AsociacionMakerLevante/Prototipo_ESP32-C3-LCD/Imagenes/S0.jpg

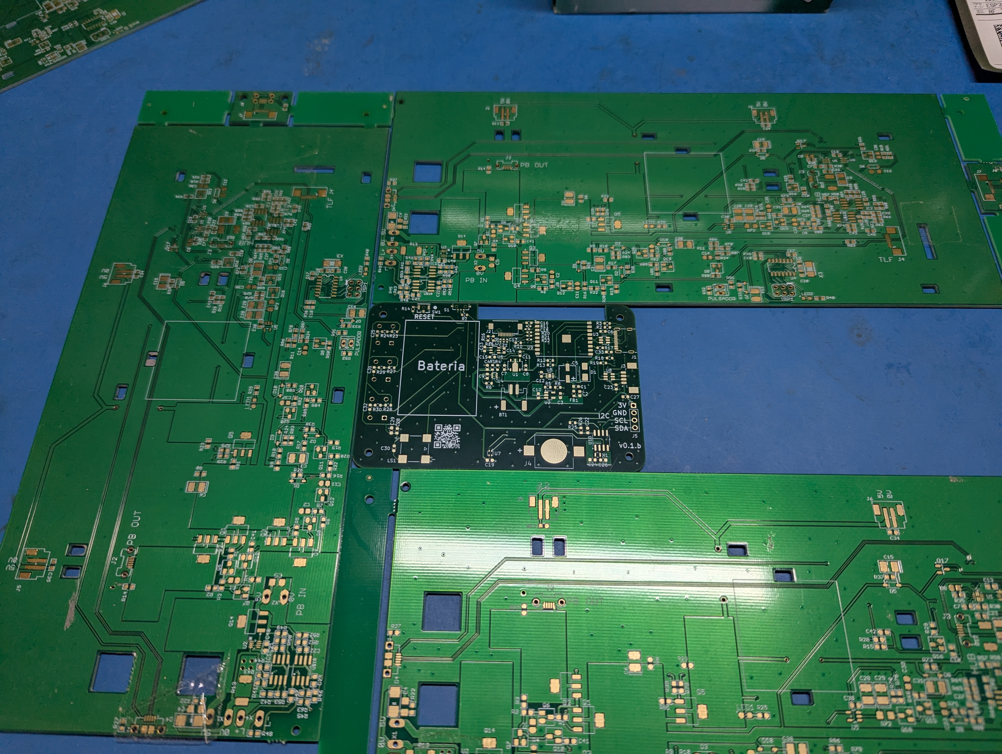
Imagenes/S0.jpg
