AsociacionMakerLevante/Prototipo_ESP32-C3-LCD/Imagenes/S00.jpg

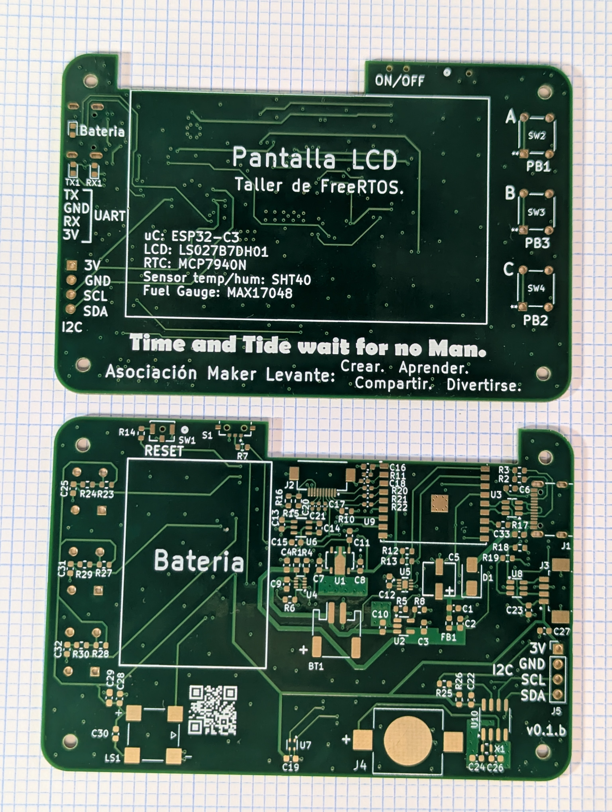
Imagenes/S00.jpg
