AsociacionMakerLevante/Prototipo_ESP32-C3-LCD/Imagenes/S1.jpg

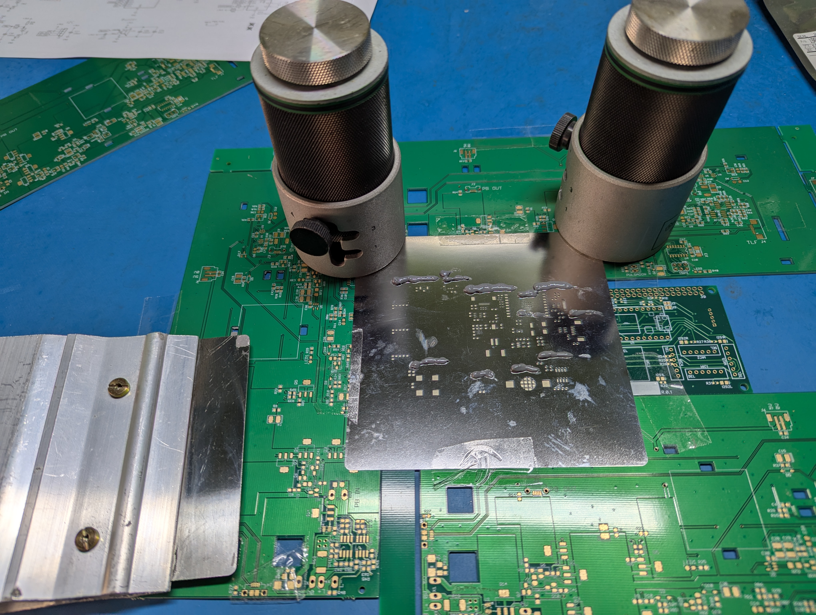
Imagenes/S1.jpg
