AsociacionMakerLevante/Prototipo_ESP32-C3-LCD/Imagenes/S4.jpg

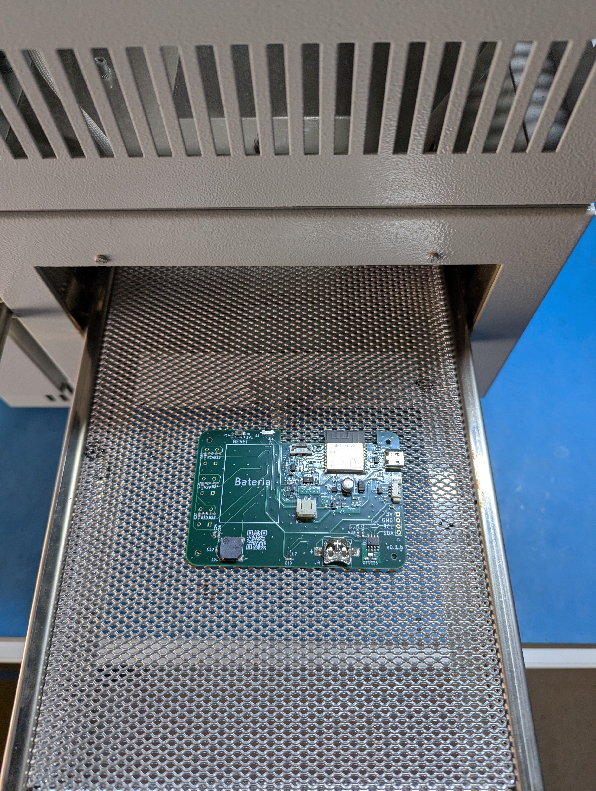
Imagenes/S4.jpg
