AsociacionMakerLevante/Prototipo_ESP32-C3-LCD/Imagenes/S6.jpg

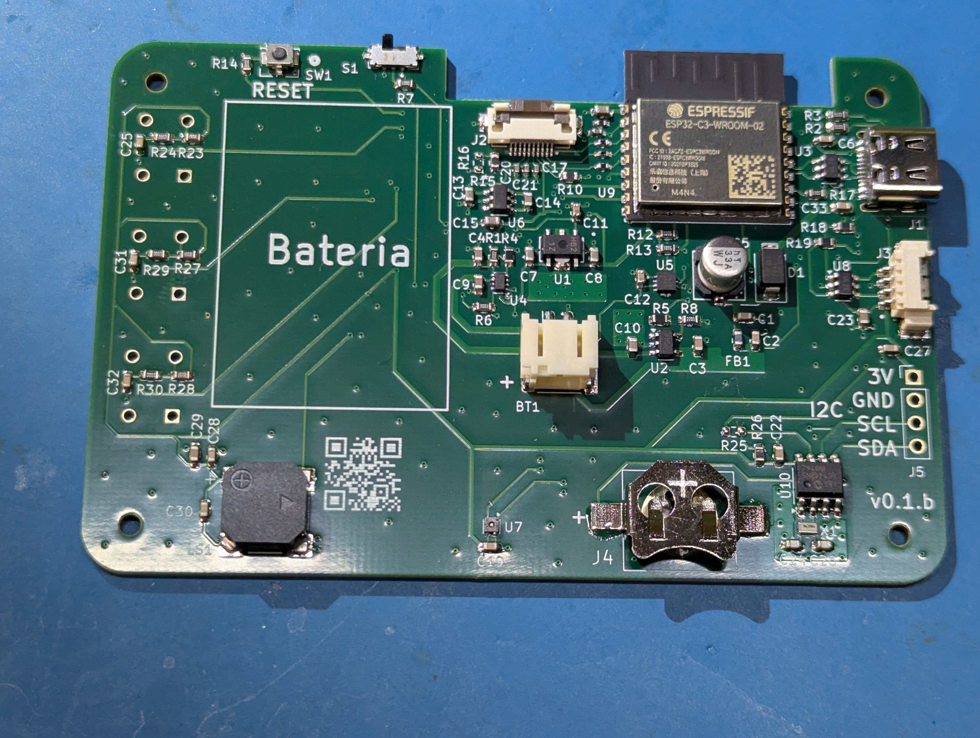
Imagenes/S6.jpg
