AsociacionMakerLevante/Prototipo_ESP32-C3-LCD/Imagenes/Bateria.jpg

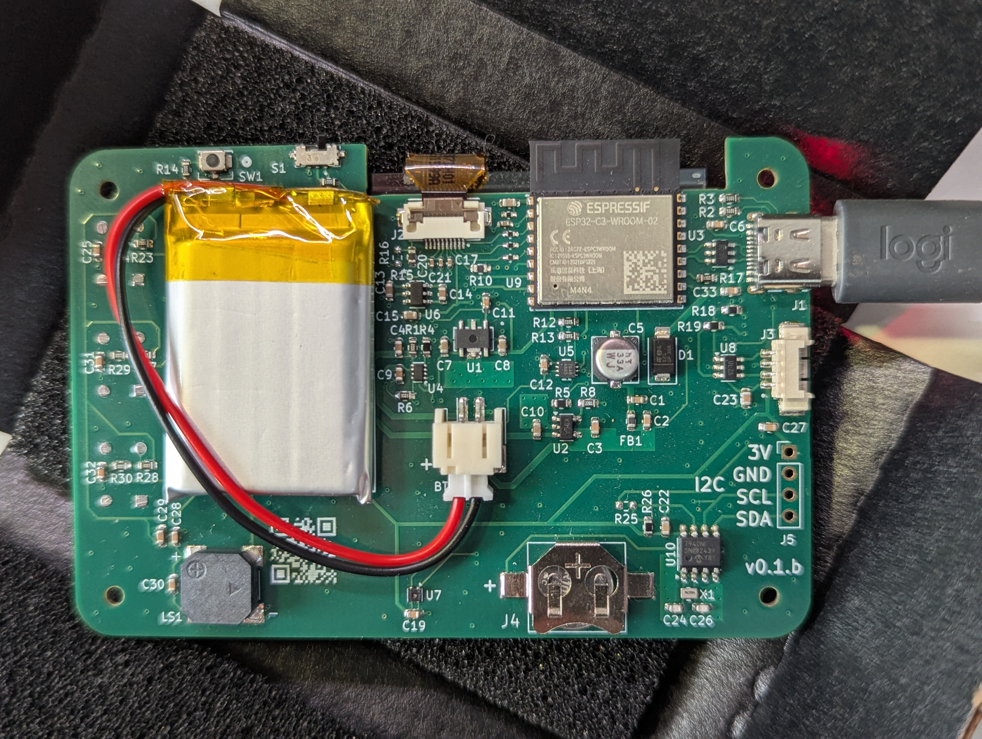
Imagenes/Bateria.jpg
